Kacafly10/BlackoutWake/electronics/bw/bw.kicad_sch

## KiCad design electronics/bw/bw.kicad_sch (2026-06-30)

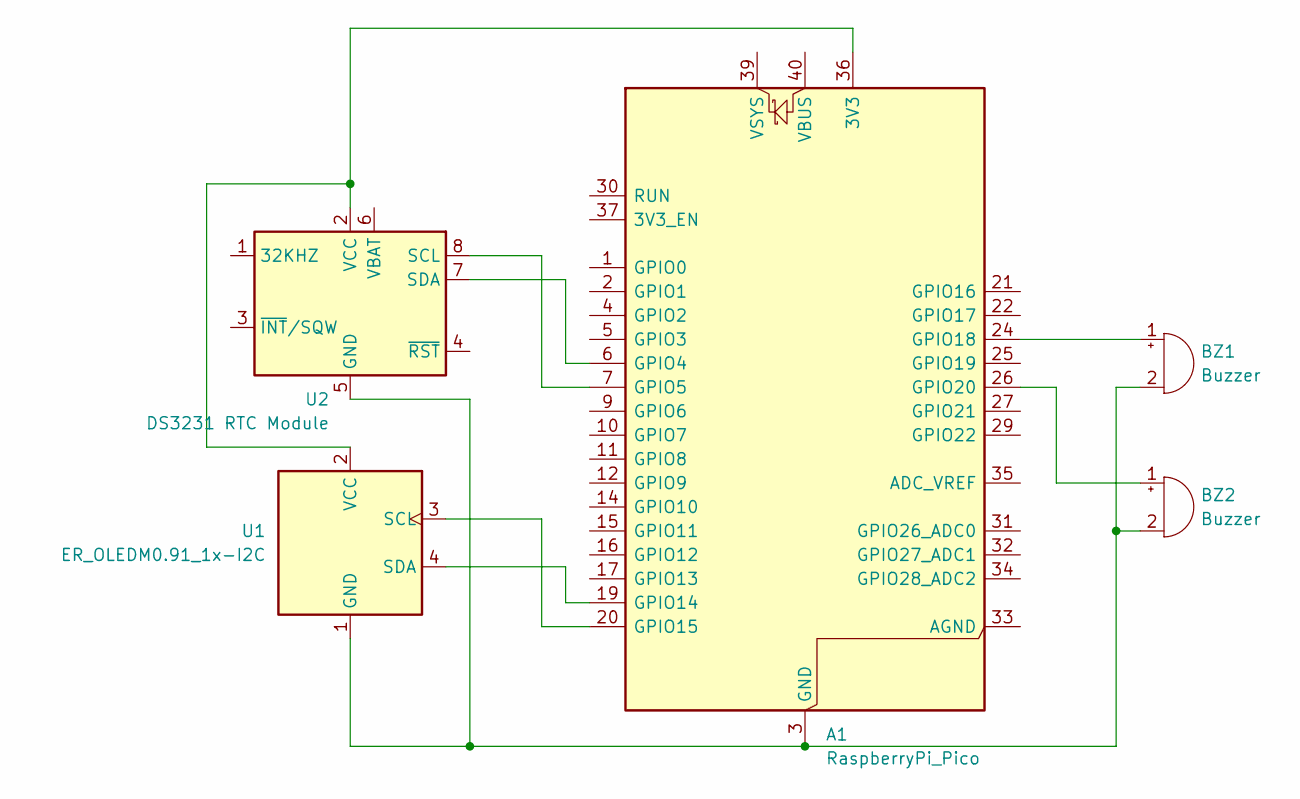
[picture p11: schematic bw.kicad_sch]

Parts:
A1: RaspberryPi_Pico; RaspberryPi_Pico_Common_Unspecified
BZ1, BZ2: Buzzer
U1: ER_OLEDM0.91_1x-I2C
U2: DS3231 RTC Module; SOIC-8_3.9x4.9mm_P1.27mm

Connections:
unnamed: A1.6 (GPIO4), U2.7 (SDA)
unnamed: A1.7 (GPIO5), U2.8 (SCL)
unnamed: A1.3 (GND), A1.8 (GND), A1.13 (GND), A1.18 (GND), A1.23 (GND), A1.28 (GND), A1.38 (GND), BZ1.2 (-), BZ2.2 (-), U1.1 (GND), U2.5 (GND)
unnamed: A1.19 (GPIO14), U1.4 (SDA)
unnamed: A1.20 (GPIO15), U1.3 (SCL)
unnamed: A1.24 (GPIO18), BZ1.1 (+)
unnamed: A1.26 (GPIO20), BZ2.1 (+)
unnamed: A1.36 (3V3), U1.2 (VCC), U2.2 (VCC)
